Bananut-Electronics/LightWand_Kosmonaut_V2/01_Documentation/00_Summary/Instagram_Kiss.jpg

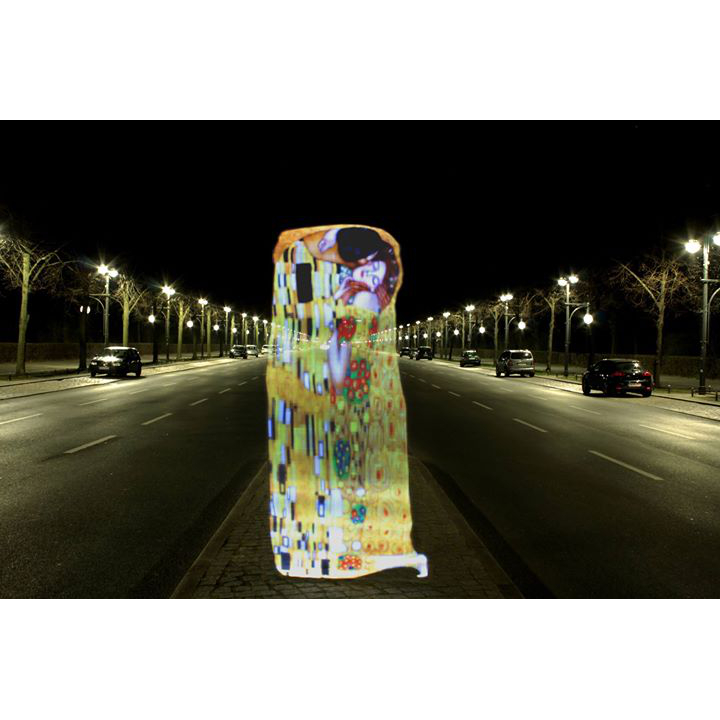
01_Documentation/00_Summary/Instagram_Kiss.jpg
