Bananut-Electronics/LightWand_Kosmonaut_V2/01_Documentation/00_Summary/Instagram_Parrot.JPG

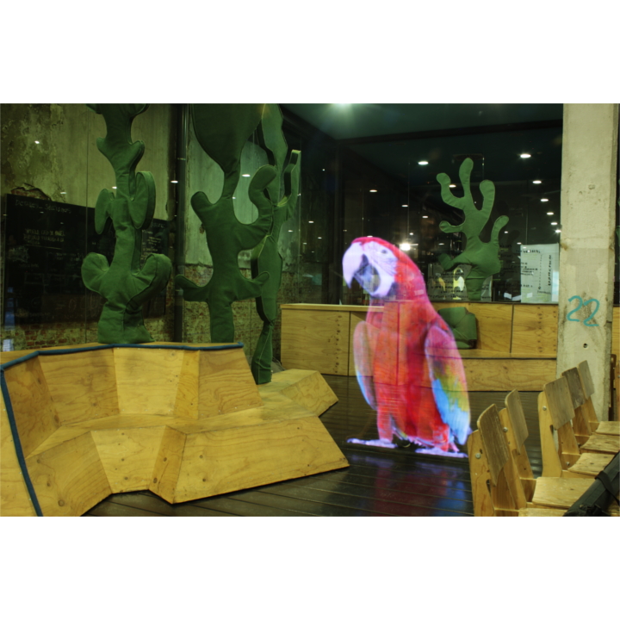
01_Documentation/00_Summary/Instagram_Parrot.JPG
