Bananut-Electronics/LightWand_Kosmonaut_V2/02_Elements/LWK2_MainBoard_Rev_1/01_HW/eagleUp/eagleUp_LWK2_MainBoard_Rev_1_board_top.png

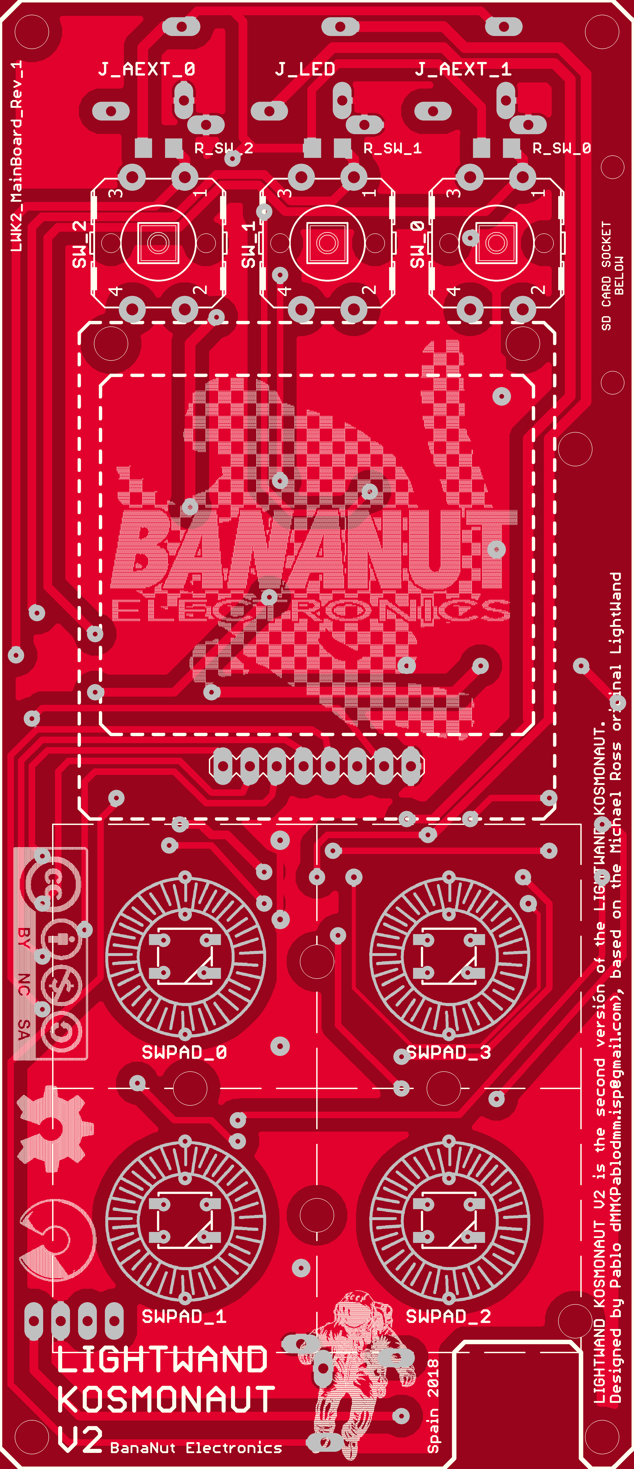
02_Elements/LWK2_MainBoard_Rev_1/01_HW/eagleUp/eagleUp_LWK2_MainBoard_Rev_1_board_top.png
