Bananut-Electronics/LightWand_Kosmonaut_V2/02_Elements/LWK2_MainBoard_Rev_1/03_Mechanics/eagleUp/eagleUp_LWK2_MainBoard_Rev_1_BOT_board_bottom.png

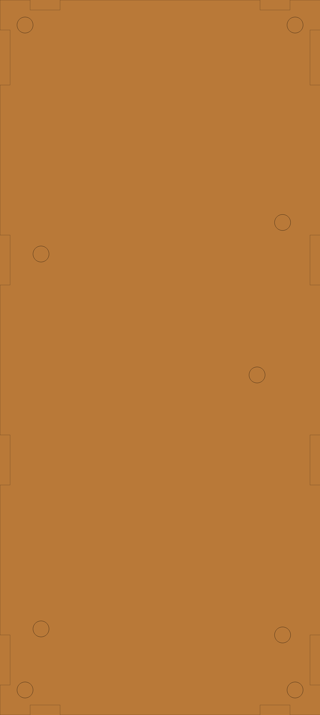
02_Elements/LWK2_MainBoard_Rev_1/03_Mechanics/eagleUp/eagleUp_LWK2_MainBoard_Rev_1_BOT_board_bottom.png
