Bananut-Electronics/LightWand_Kosmonaut_V2/03_Resources/LWK2_SampleImages_BMP_144/MONKEY.bmp

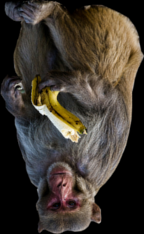
03_Resources/LWK2_SampleImages_BMP_144/MONKEY.bmp
