Bananut-Electronics/LightWand_Kosmonaut_V2/03_Resources/LWK2_SampleImages_BMP_144/OBoffil_0.bmp

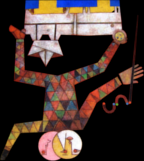
03_Resources/LWK2_SampleImages_BMP_144/OBoffil_0.bmp
