Bananut-Electronics/LightWand_Kosmonaut_V2/01_Documentation/00_Summary/LWKed_Materials - copia.png

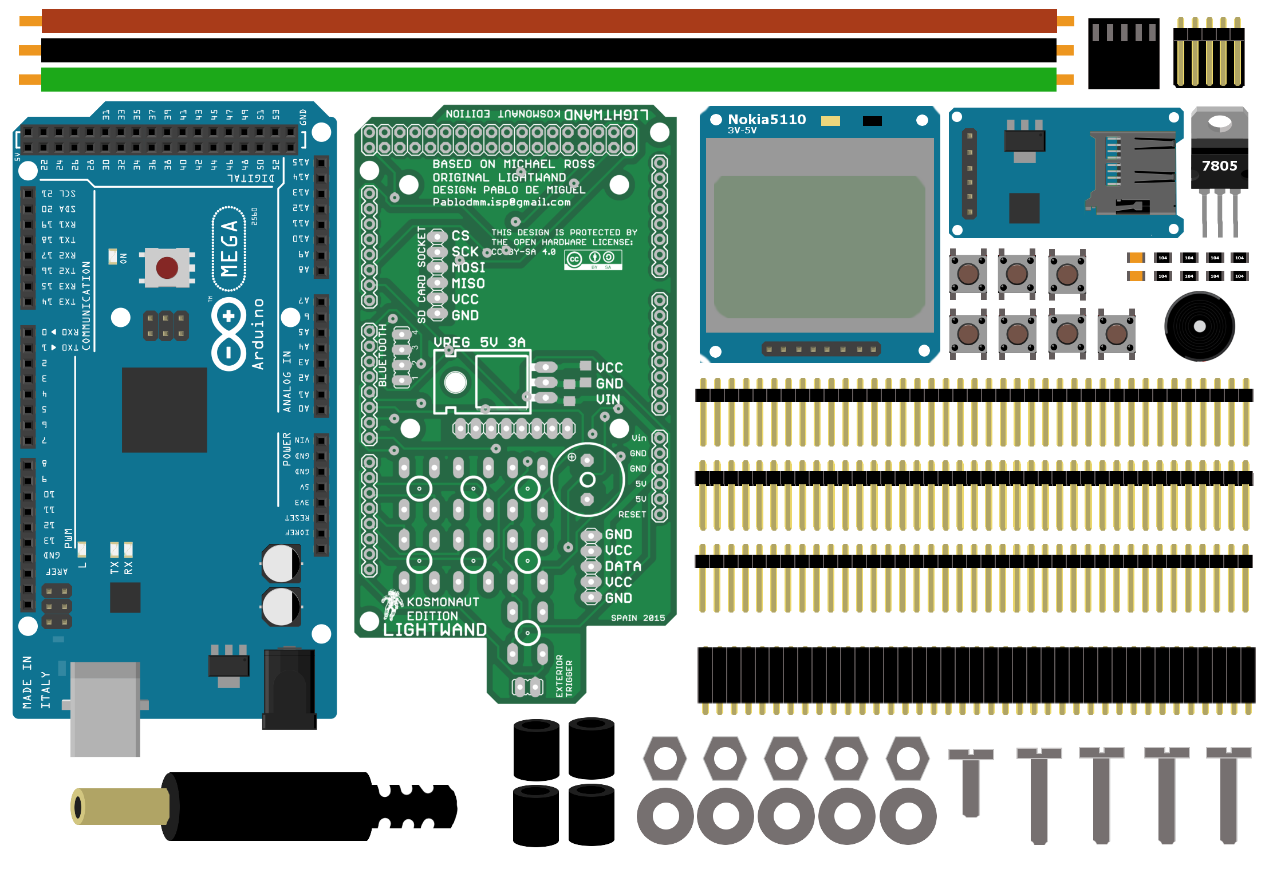
01_Documentation/00_Summary/LWKed_Materials - copia.png
