Bananut-Electronics/LightWand_Kosmonaut_V2/03_Resources/LWK2_ComponentImages/5pin_MaleHead.png

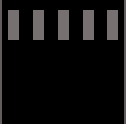
03_Resources/LWK2_ComponentImages/5pin_MaleHead.png
