Bananut-Electronics/LightWand_Kosmonaut_V2/03_Resources/LWK2_ComponentImages/ArduinoMega - copia.png

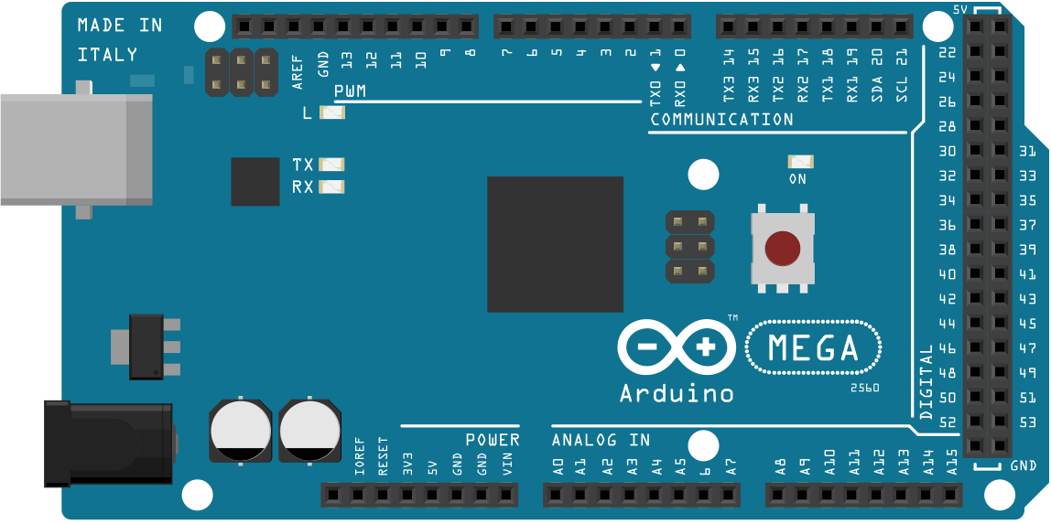
03_Resources/LWK2_ComponentImages/ArduinoMega - copia.png
