Bananut-Electronics/LightWand_Kosmonaut_V2/03_Resources/LWK2_ComponentImages/MicroSD_Socket - copia.png

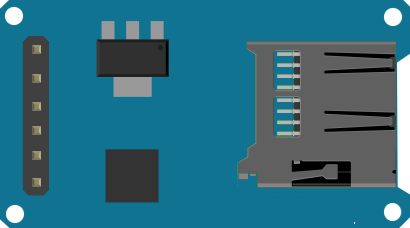
03_Resources/LWK2_ComponentImages/MicroSD_Socket - copia.png
