Bananut-Electronics/LightWand_Kosmonaut_V2/03_Resources/LWK2_ComponentImages/Nokia5110Screen - copia.png

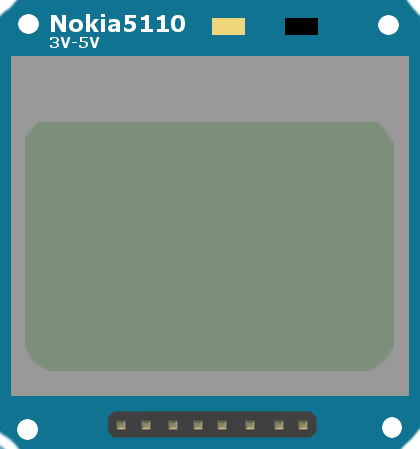
03_Resources/LWK2_ComponentImages/Nokia5110Screen - copia.png
