Bananut-Electronics/LightWand_Kosmonaut_V2/03_Resources/LWK2_ComponentImages/pin - copia.png

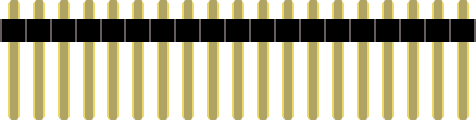
03_Resources/LWK2_ComponentImages/pin - copia.png
