Bananut-Electronics/LightWand_Kosmonaut_V2/01_Documentation/00_Summary/LK_V1_Assembled.PNG

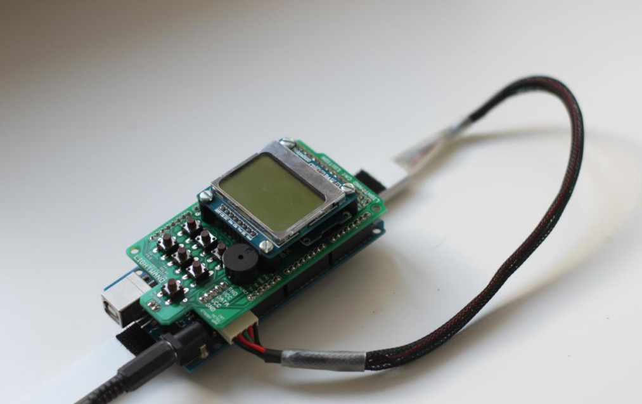
01_Documentation/00_Summary/LK_V1_Assembled.PNG
