Bananut-Electronics/LightWand_Kosmonaut_V2/01_Documentation/01_GIMPGuide/LWK2_GIMP_15.png

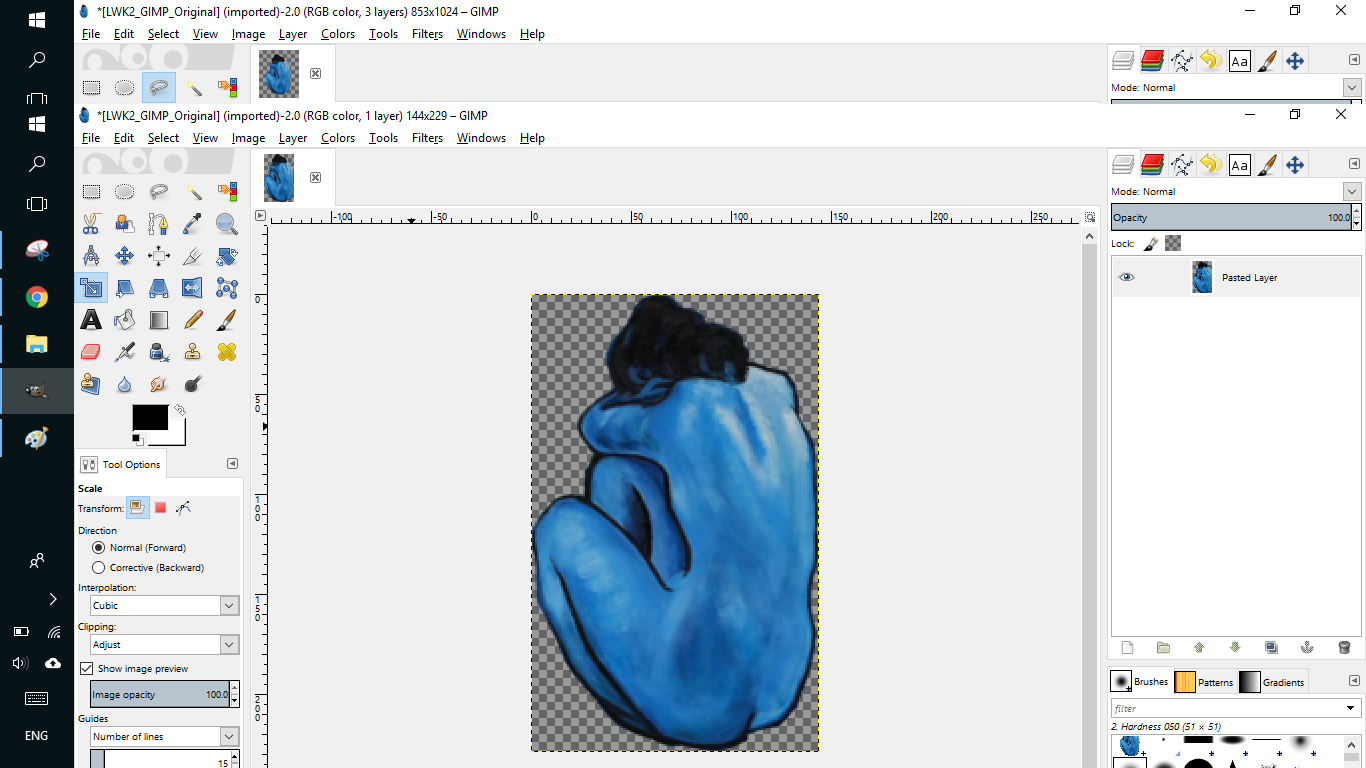
01_Documentation/01_GIMPGuide/LWK2_GIMP_15.png
