Bananut-Electronics/LightWand_Kosmonaut_V2/03_Resources/LWK2_SampleImages_BMP_144/TEST_PTT.bmp

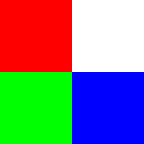
03_Resources/LWK2_SampleImages_BMP_144/TEST_PTT.bmp
